zzjlamb/days2bin/peripherals/glowbit.c

#include <stdlib.h>
#include <string.h>
#include "hardware/pio.h"
#include "ds3231.h"
#include "ws2812.pio.h"

#include "font.h"
#include "GPIO_pin_assignments.h"
#include "glowbit.h"

#define IS_RGBW false // Glowbit uses WS2812B RGB 8 bits each ie 24 bits
#define NUM_PIXELS 64 // Glowbit Matrix 8x8 uses an 8x8 matrix
#define NUM_COLUMNS 8
#define NUM_ROWS 8
#define SPACE_CHAR 0x20

uint32_t display_buffer[NUM_ROWS][NUM_COLUMNS];

static inline void put_pixel(uint32_t pixel_grb)
{
    pio_sm_put_blocking(pio0, 0, pixel_grb << 8u);
}

static inline uint32_t urgb_u32(uint8_t r, uint8_t g, uint8_t b)
{
    return ((uint32_t)(r) << 8) |
           ((uint32_t)(g) << 16) |
           (uint32_t)(b);
}

/* Initialise the glowbit matrix    */
/*                                  */
void glowbit_init()
{
    PIO pio = pio0;
    int sm = 0;
    uint offset = pio_add_program(pio, &ws2812_program);

    ws2812_program_init(pio, sm, offset, WS2812_PIN, 800000, IS_RGBW);
}

/* Fill the glowbit buffer with black pixels    */
/*                                              */
void pattern_black()
{
    for (int i = 0; i < NUM_ROWS; ++i)
        for (int j = 0; j < NUM_COLUMNS; j++)
            display_buffer[i][j] = 0;
}

/* Send the buffer to the glowbit matrix    */
/*                                          */
void glowbit_show()
{
    for (int i = 0; i < NUM_ROWS; ++i)
        for (int j = 0; j < NUM_COLUMNS; j++)
            put_pixel(display_buffer[i][j]);
}

/* Fill glowbit buffer with zeros and send to device    */
/*                                                      */
void glowbit_clearScreen()
{
    pattern_black();
    glowbit_show();
}

/* Draw a char to the glowbit buffer    */
/*                                      */
void glowbit_drawChar(char ch, uint32_t colour)
{
    if (ch > 127)
        ch = '.';
    int fMapOffset = (ch - SPACE_CHAR) * 8;
    int display_cursorX = 0;
    for (int i = fMapOffset; i < fMapOffset + 8; i++)
    {
        int8_t column = fontmap[i];
        for (int display_cursorY = 0; display_cursorY < 8; display_cursorY++)
        {
            bool pixel = (column << display_cursorY) & 0b10000000;
            display_buffer[7 - display_cursorY][display_cursorX] = pixel ? colour : 0;
        }
        display_cursorX++;
        display_cursorX %= 8;
    }
}

/* Scroll text on glowbit 1 pixel to left   */
/* Writes buffer to device immediately      */
void glowbit_scrollText(char * text, uint32_t colour)
{
    int textLength = strlen(text);

    /* Do nothing if null string */
    if (textLength == 0)
        return;

    /* Repeat code below eight times for each character, including the terminating null */
    for (int xDone = 0; xDone < (textLength + 1) * 8; xDone++)
    {

        /*  Shift one column to left */
        for (int x = 1; x < 8; x++)
        {
            for (int y = 0; y < 8; y++)
            {
                display_buffer[y][x - 1] = display_buffer[y][x];
            }
        }
        char currentChar = text[xDone / 8];
        if (currentChar == 0)
            currentChar = SPACE_CHAR;       // to flush last character in string off the display

        if (currentChar > 127)
            currentChar = '.';              // render out of range char as a '.'

        int columnIndex = xDone % 8;
        int fMapOffset = (currentChar - SPACE_CHAR) * 8 + columnIndex;
        int8_t column = fontmap[fMapOffset];
        for (int display_cursorY = 0; display_cursorY < 8; display_cursorY++)
        {
            bool pixel = (column << display_cursorY) & 0b10000000;
            display_buffer[7 - display_cursorY][7] = pixel ? colour : 0;
        }
        glowbit_show();
        sleep_ms(100);
    }
}
